4ms/QPLFO-v22/src/adc.c

/*
 * adc.c - adc setup
 */
 
#include "adc.h"

void init_adc(uint16_t *ADC_Buffer)
{
	DMA_InitTypeDef DMA_InitStructure;
	ADC_InitTypeDef ADC_InitStructure;
	GPIO_InitTypeDef GPIO_InitStructure;

	/* enable clocks for DMA2, ADC1 ----------------------------------*/
	RCC_AHBPeriphClockCmd(RCC_AHBPeriph_DMA1, ENABLE);
	RCC_APB2PeriphClockCmd(RCC_APB2Periph_ADC1, ENABLE);

	/* DMA2 stream4 channel0 configuration ----------------------------------*/
	DMA_InitStructure.DMA_PeripheralBaseAddr = (uint32_t)&ADC1->DR;
	DMA_InitStructure.DMA_MemoryBaseAddr = (uint32_t)ADC_Buffer;
	DMA_InitStructure.DMA_DIR = DMA_DIR_PeripheralSRC;
	DMA_InitStructure.DMA_BufferSize = 4;
	DMA_InitStructure.DMA_PeripheralInc = DMA_PeripheralInc_Disable;
	DMA_InitStructure.DMA_MemoryInc = DMA_MemoryInc_Enable;
	DMA_InitStructure.DMA_PeripheralDataSize = DMA_PeripheralDataSize_HalfWord;
	DMA_InitStructure.DMA_MemoryDataSize = DMA_MemoryDataSize_HalfWord;
	DMA_InitStructure.DMA_Mode = DMA_Mode_Circular;
	DMA_InitStructure.DMA_Priority = DMA_Priority_High;
	DMA_Init(DMA1_Channel1, &DMA_InitStructure);
	DMA_Cmd(DMA1_Channel1, ENABLE);

	/* ADC1 Init ------------------------------------------------------------*/
	ADC_DeInit(ADC1);
	ADC_InitStructure.ADC_Resolution = ADC_Resolution_12b;
	ADC_InitStructure.ADC_ContinuousConvMode = ENABLE;
	ADC_InitStructure.ADC_ExternalTrigConvEdge = ADC_ExternalTrigConvEdge_None;
	ADC_InitStructure.ADC_ExternalTrigConv = ADC_ExternalTrigConv_T1_TRGO;
	ADC_InitStructure.ADC_DataAlign = ADC_DataAlign_Right;
	ADC_InitStructure.ADC_ScanDirection = ADC_ScanDirection_Upward;
	ADC_Init(ADC1, &ADC_InitStructure);
	
	/* Configure analog input pins ------------------------------------------*/
	RCC_AHBPeriphClockCmd(RCC_AHBPeriph_GPIOA, ENABLE);

	GPIO_InitStructure.GPIO_Mode = GPIO_Mode_AN;
	GPIO_InitStructure.GPIO_PuPd = GPIO_PuPd_NOPULL ;
	GPIO_InitStructure.GPIO_Pin = GPIO_Pin_0 | GPIO_Pin_1 | GPIO_Pin_2 | GPIO_Pin_3;
	GPIO_Init(GPIOA, &GPIO_InitStructure);

	ADC_ChannelConfig(ADC1, ADC_Channel_0, ADC_SampleTime_71_5Cycles);
	ADC_ChannelConfig(ADC1, ADC_Channel_1, ADC_SampleTime_71_5Cycles);
	ADC_ChannelConfig(ADC1, ADC_Channel_2, ADC_SampleTime_71_5Cycles);
	ADC_ChannelConfig(ADC1, ADC_Channel_3, ADC_SampleTime_71_5Cycles);
	
	//ADC_DMARequestAfterLastTransferCmd(ADC1, ENABLE);
	ADC_DMARequestModeConfig(ADC1, ADC_DMAMode_Circular);
//	ADC_ContinuousModeCmd(ADC1, ENABLE);
	ADC_DMACmd(ADC1, ENABLE);
	ADC_Cmd(ADC1, ENABLE);
	ADC_StartOfConversion(ADC1);
}
